Berlodu13/Ventury-vacuum-module/Docs/vue de droite.png

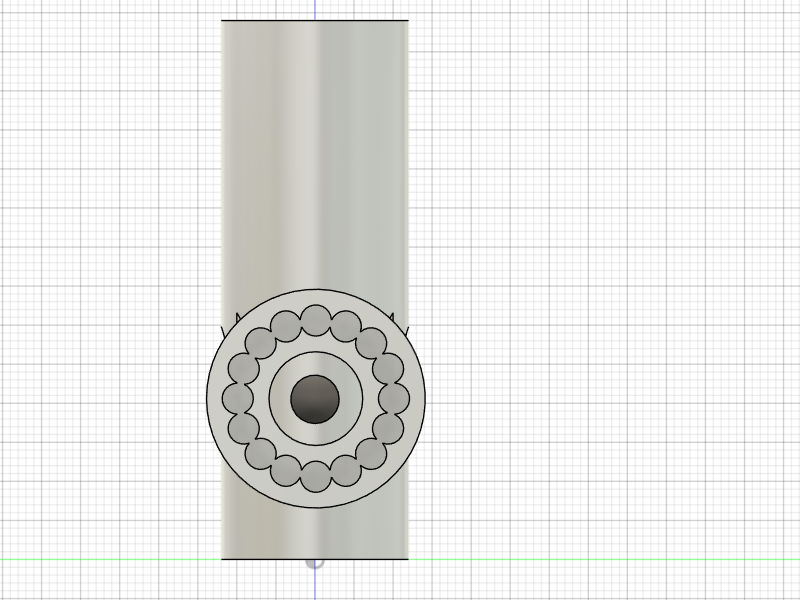
Docs/vue de droite.png
